vladdpaunescu/tars-robot/docs/photos/IMG_1185.JPG

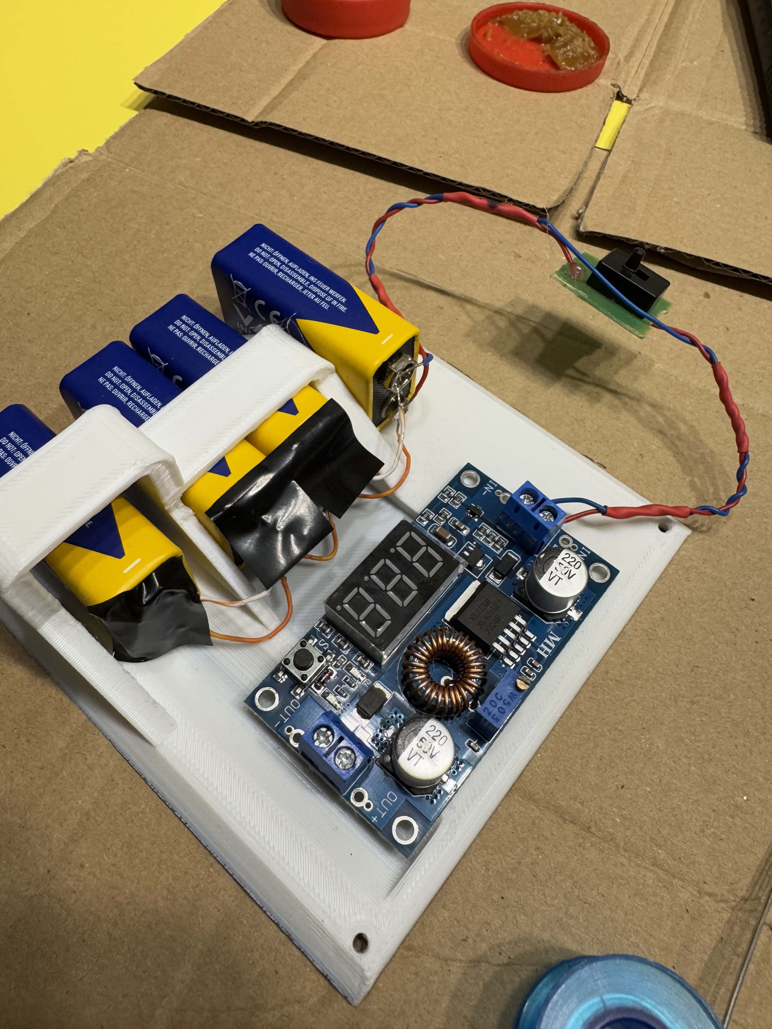
docs/photos/IMG_1185.JPG
