vladdpaunescu/tars-robot/docs/photos/IMG_1186.JPG

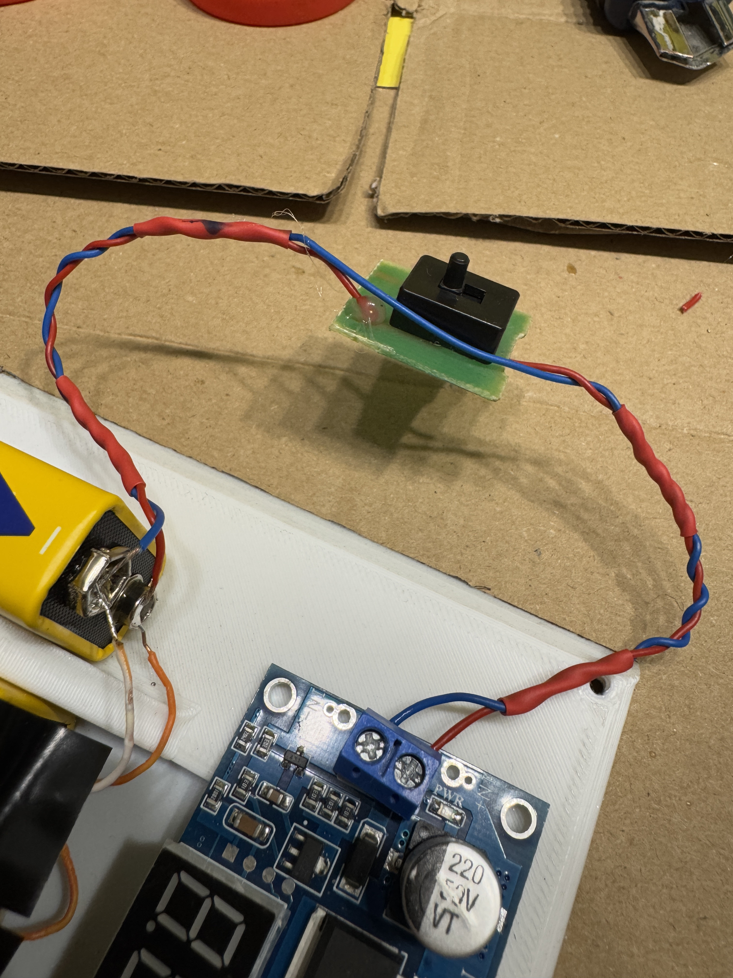
docs/photos/IMG_1186.JPG
