vladdpaunescu/tars-robot/cad/BODY/lowerLid - 1buc.stl

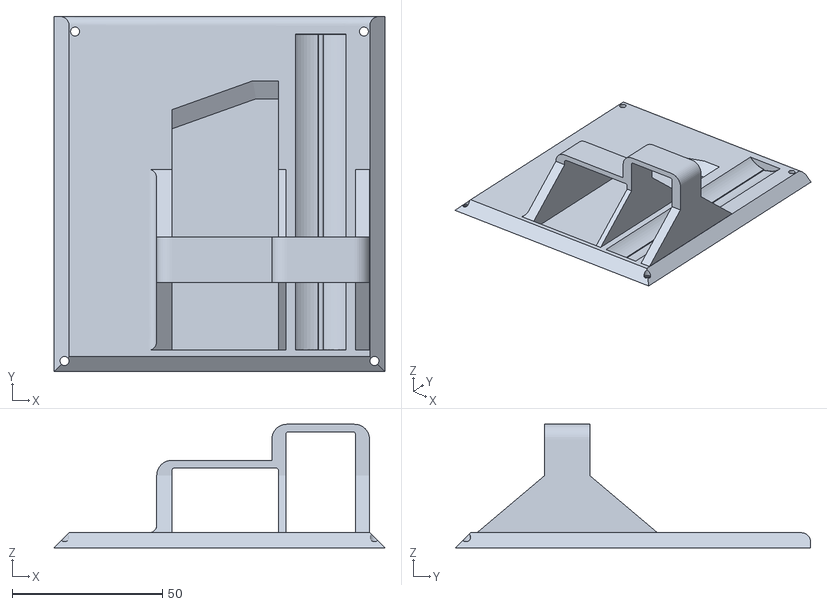
[picture p37: CAD file, 2026-09-02]
cad/BODY/lowerLid - 1buc.stl
110.0 x 118.0 x 41.1
