vladdpaunescu/tars-robot/cad/FOOTS/armsBoth.stl

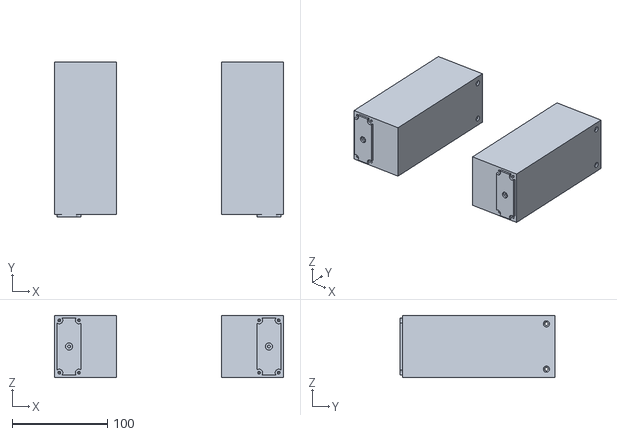
[picture p38: CAD file, 2026-09-02]
cad/FOOTS/armsBoth.stl
240.0 x 162.0 x 65.0
