vladdpaunescu/tars-robot/cad/BODY/suspension/verticalServoClip - 1buc.stl

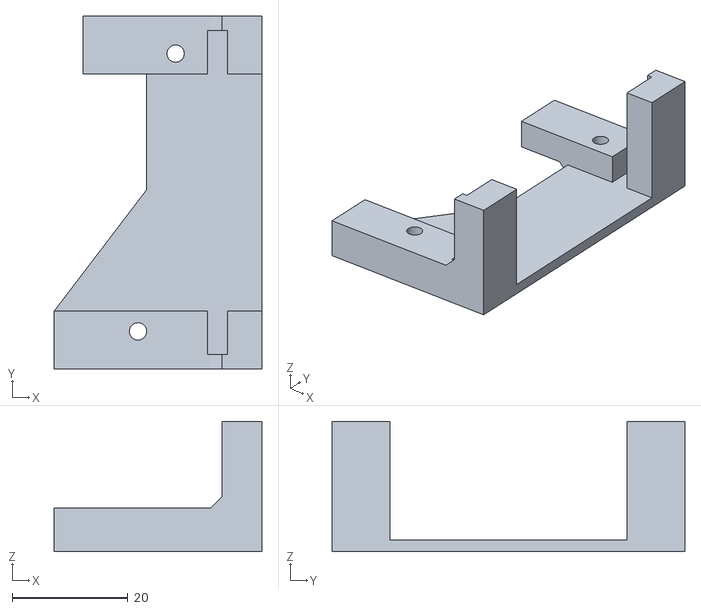
[picture p39: CAD file, 2026-09-02]
cad/BODY/suspension/verticalServoClip - 1buc.stl
35.9 x 61.0 x 22.5
