vladdpaunescu/tars-robot/cad/FOOTS/hulls.stl

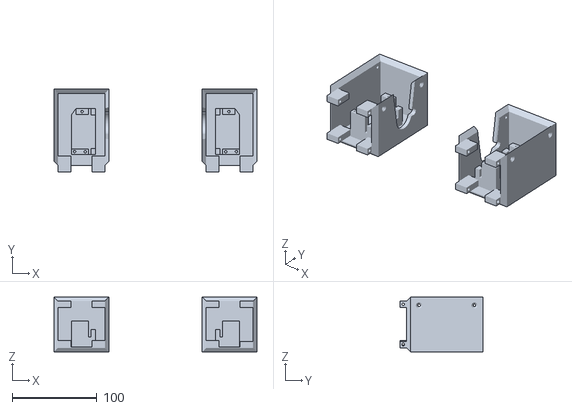
[picture p40: CAD file, 2026-09-02]
cad/FOOTS/hulls.stl
240.0 x 98.0 x 65.0
