vladdpaunescu/tars-robot/cad/BODY/suspension/spacer - 1buc.stl

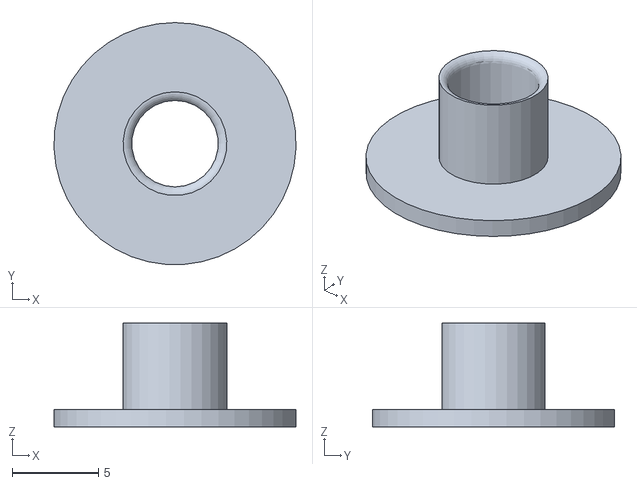
[picture p41: CAD file, 2026-09-02]
cad/BODY/suspension/spacer - 1buc.stl
14.0 x 14.0 x 6.00
