vladdpaunescu/tars-robot/cad/BODY/suspension/suspensionMountRight - 1buc.stl

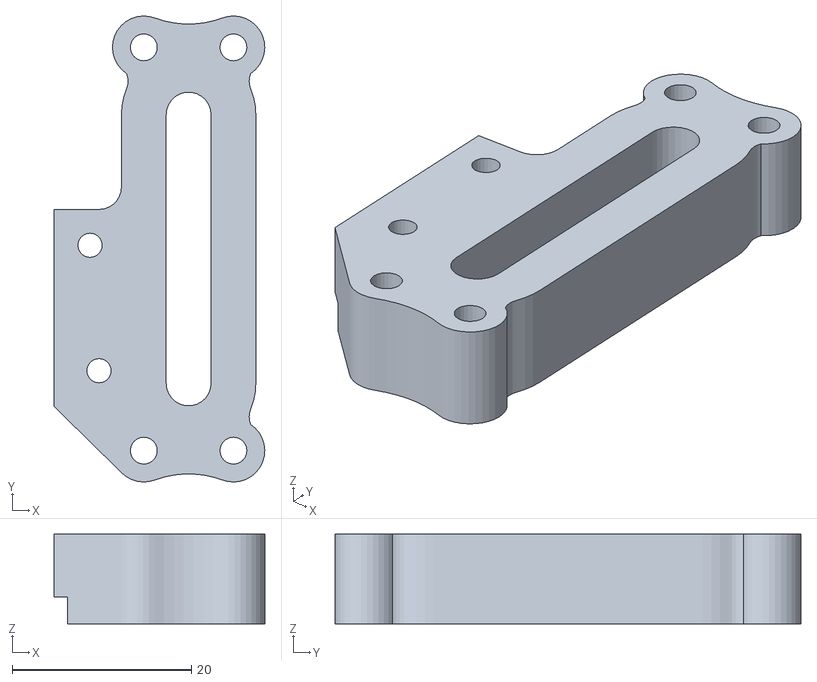
[picture p42: CAD file, 2026-09-02]
cad/BODY/suspension/suspensionMountRight - 1buc.stl
23.5 x 52.0 x 10.0
