vladdpaunescu/tars-robot/cad/BODY/suspension/suspensionMountleft - 1buc.stl

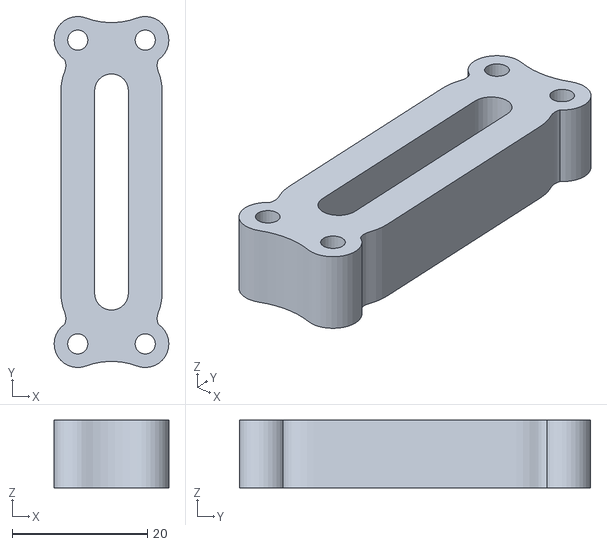
[picture p43: CAD file, 2026-09-02]
cad/BODY/suspension/suspensionMountleft - 1buc.stl
17.0 x 52.0 x 10.0
