vladdpaunescu/tars-robot/docs/photos/IMG_1140.JPG

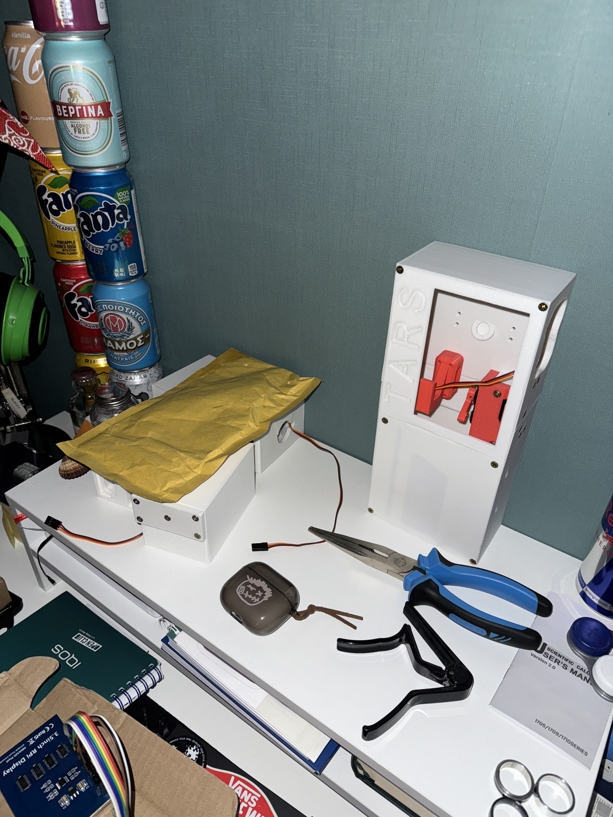
docs/photos/IMG_1140.JPG
