vladdpaunescu/tars-robot/docs/photos/IMG_1146.JPG

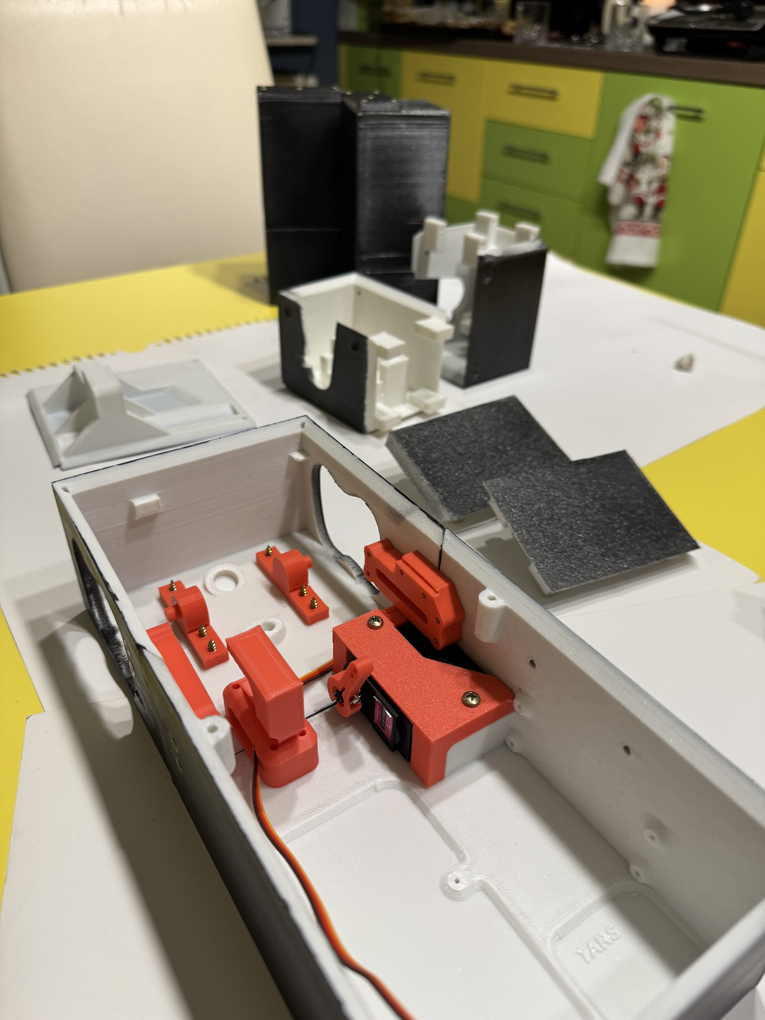
docs/photos/IMG_1146.JPG
