vladdpaunescu/tars-robot/docs/photos/IMG_1147.JPG

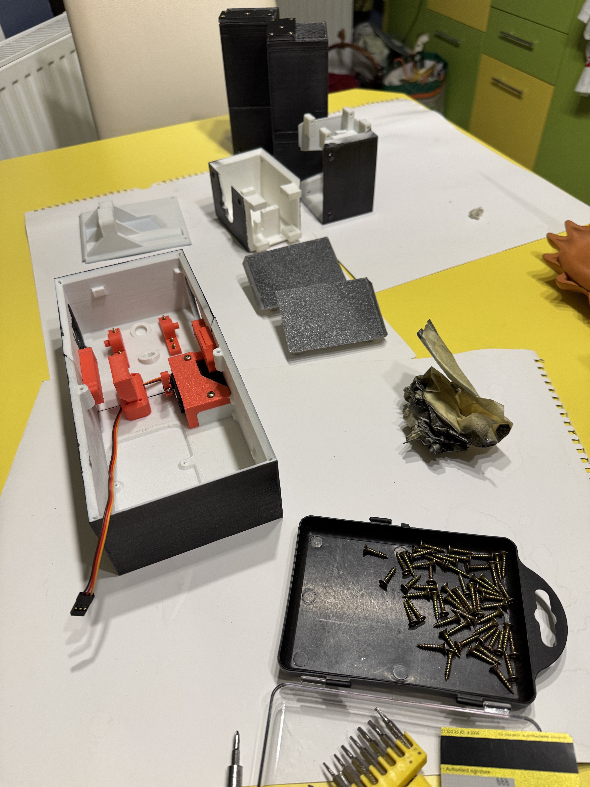
docs/photos/IMG_1147.JPG
