vladdpaunescu/tars-robot/docs/photos/IMG_1187.JPG

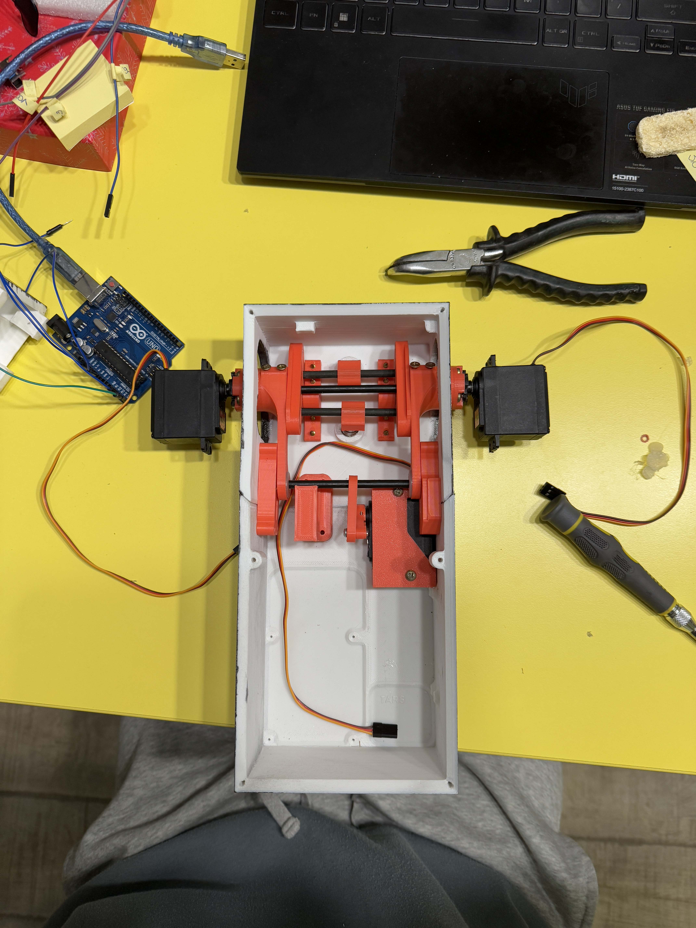
docs/photos/IMG_1187.JPG
