vladdpaunescu/tars-robot/docs/photos/IMG_1191.JPG

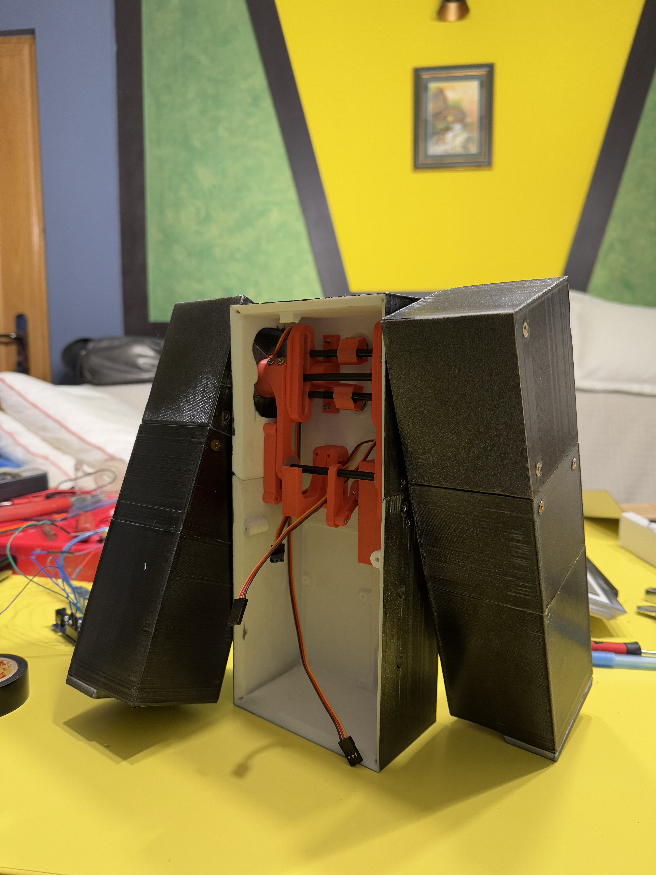
docs/photos/IMG_1191.JPG
