vladdpaunescu/tars-robot/docs/photos/IMG_1192.JPG

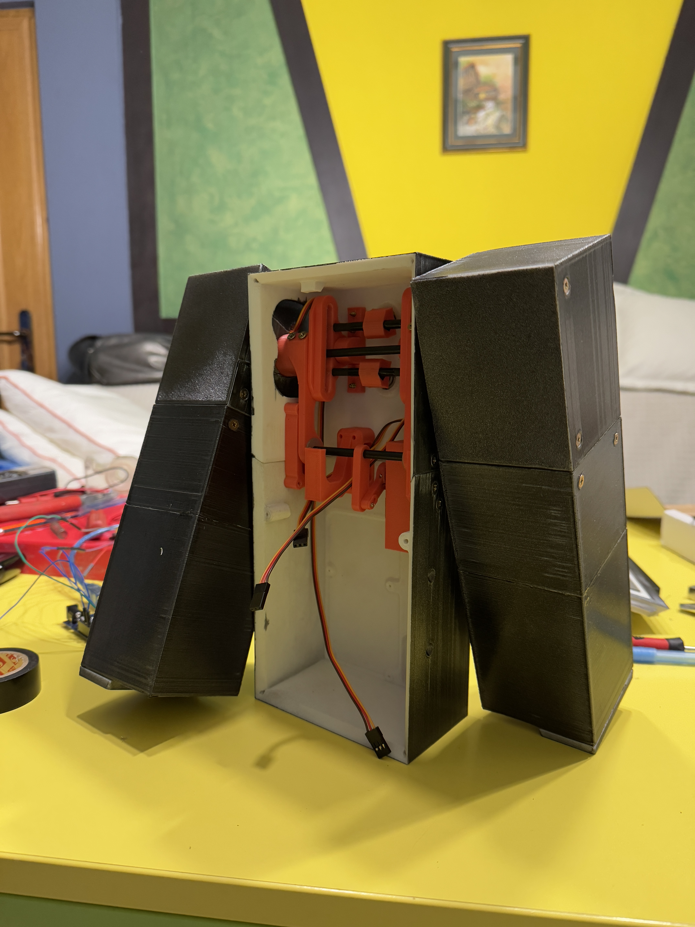
docs/photos/IMG_1192.JPG
