vladdpaunescu/tars-robot/docs/photos/IMG_1193.JPG

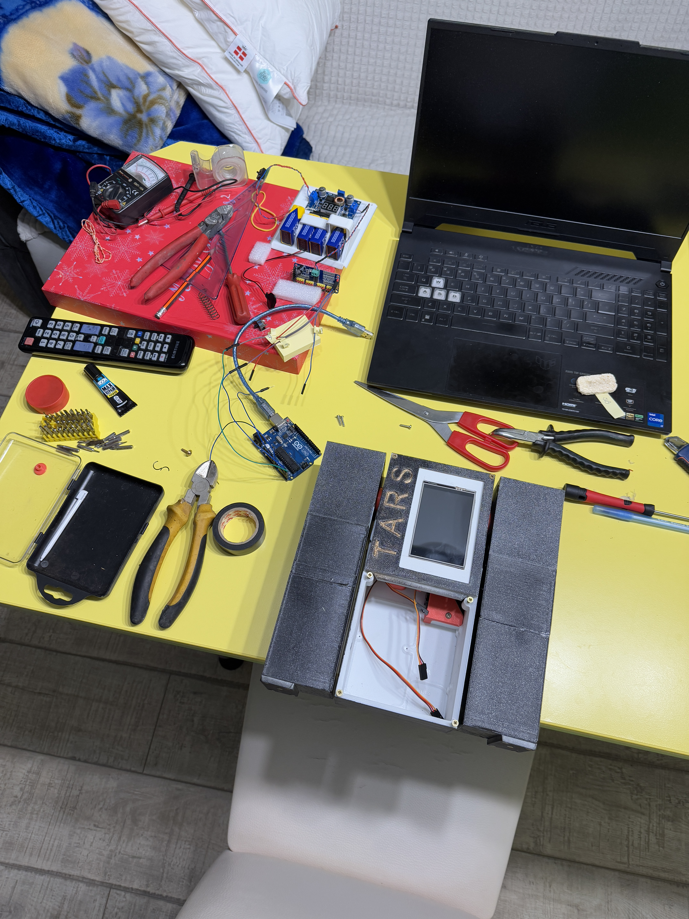
docs/photos/IMG_1193.JPG
